kb1lqd/ADA4610-Transimpedance-Amplifier-REV-1.0/Simulation/TIA_Preamp_Unipolar.asc

C2: cap; 10p
I1: current; AC 1
R1: res; 10k
R4: res; 20
R7: res; 1k
R8: res; 50k
R9: res; 50
R10: res; 50
U1: AD8067
U2: AD8067
V1: voltage; 5
V2: voltage; -5
V3: voltage; 10
Named nets: 0, +5V, -5V, Vout_NRB_Bipolar, +10V
.ac dec 100 1 100MEG
Bipolar Operation
Unipolar Operation
