kb1lqd/ADA4610-Transimpedance-Amplifier-REV-1.0/Simulation/LM833N_Headphone.asc

C1: cap; 100n
C3: cap; 1µ
R1: res; 50
R2: res; 10k
R3: res; 10k
R4: res; 50
R7: res; 1k
R8: res; 20k
R10: res; 8
U3: ADA4610
V1: voltage; 5
V2: voltage; -5
V3: voltage; 10
V4: voltage; SINE(0 10m 10k)
Named nets: 0, +5V, -5V, +10V, Vbias
.tran 0 1m 0 1u
Bipolar Operation
Unipolar Operation
Estimated Dark Current
