kb1lqd/ADA4610-Transimpedance-Amplifier-REV-1.0/Simulation/TIA_Preamp_Linedriver_AC.asc

C1: cap; 33p
C2: cap; 3.3p
C3: cap; 10µ
I1: current; AC 1
R1: res; 100k
R4: res; 20
R7: res; 1k
R8: res; 50k
R9: res; 50
R10: res; 50
U1: ADA4610
U3: ADA4610
V1: voltage; 5
V2: voltage; -5
V3: voltage; 10
Named nets: 0, +5V, -5V, Vout_NRB_Bipolar, +10V
.ac dec 100 1 100MEG
Bipolar Operation
Unipolar Operation
