kb1lqd/ADA4610-Transimpedance-Amplifier-REV-1.0/Simulation/TIA_Preamp_Linedriver_ADA4637-1.asc

C1: cap; 100n
C2: cap; 10p
C3: cap; 10µ
C4: cap; 10p
C5: cap; 10µ
I1: current; AC 1
I2: current; AC 1
R1: res; 100k
R2: res; 10k
R3: res; 10k
R4: res; 20
R5: res; 100k
R6: res; 20
R7: res; 10k
R8: res; 500k
R9: res; 50
R10: res; 50
R11: res; 10k
R12: res; 500k
R13: res; 50
R14: res; 50
T1: tline; Td=5u Z0=50
T2: tline; Td=5u Z0=50
U1: ADA4610
U2: ADA4637
U3: ADA4610
U4: ADA4637
V1: voltage; 5
V2: voltage; -5
V3: voltage; 10
Named nets: 0, +5V, -5V, +10V, Vbias, Vout_NRB_Bipolar
.ac dec 100 10 100MEG
Bipolar Operation
Unipolar Operation
Estimated Dark Current
Estimated Dark Current
