kb1lqd/ADA4610-Transimpedance-Amplifier-REV-1.0/Simulation/TIA_Preamp_Linedriver.asc

C1: cap; 100n
C2: cap; 10p
C3: cap; 1µ
I1: current; SINE(100n 100n 20k 1u)
R1: res; 100k
R2: res; 10k
R3: res; 10k
R4: res; 20
R7: res; 10k
R8: res; 500k
R9: res; 50
R10: res; 50
T1: tline; Td=5u Z0=50
U1: ADA4610
U3: ADA4610
V1: voltage; 5
V2: voltage; -5
V3: voltage; 10
Named nets: 0, +5V, -5V, +10V, Vbias, Vout_NRB_Bipolar
.tran 0 1m 0 1u
Bipolar Operation
Unipolar Operation
Estimated Dark Current
